rutony/RutonyPad/assets/images/2.webp

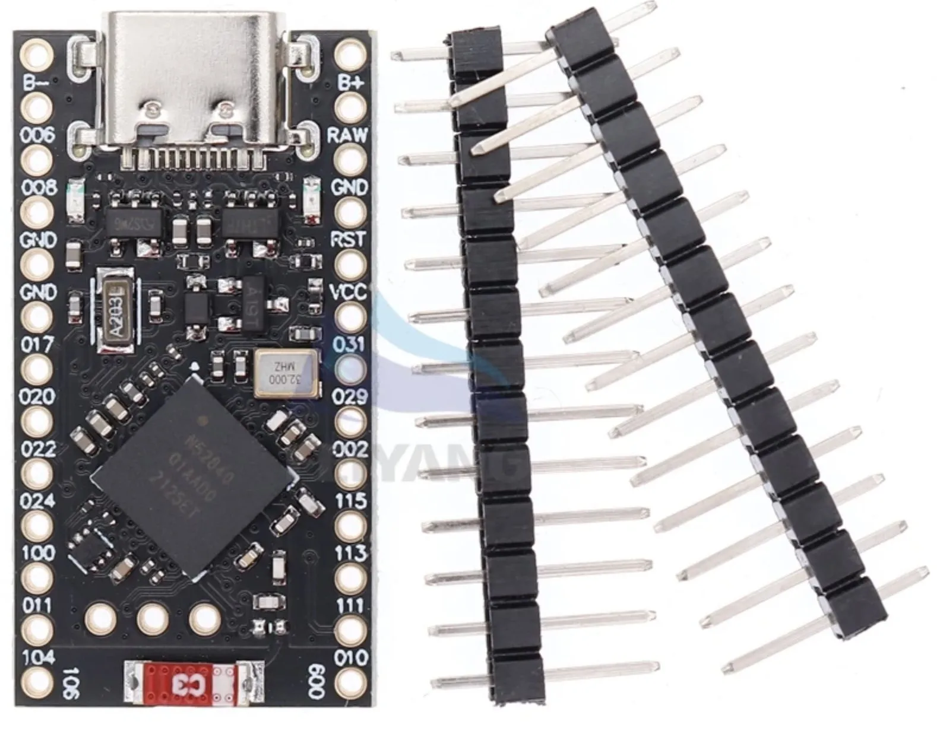
assets/images/2.webp
