rutony/RutonyPad/assets/images/3.jpg

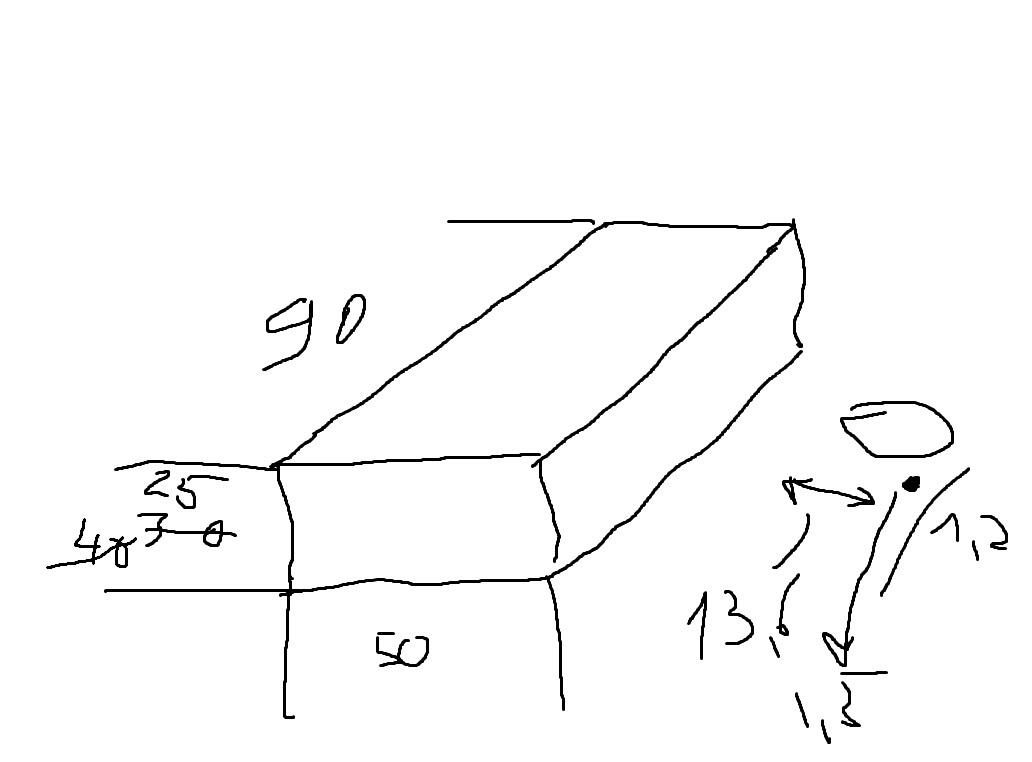
assets/images/3.jpg
