rutony/RutonyPad/assets/images/4.jpg

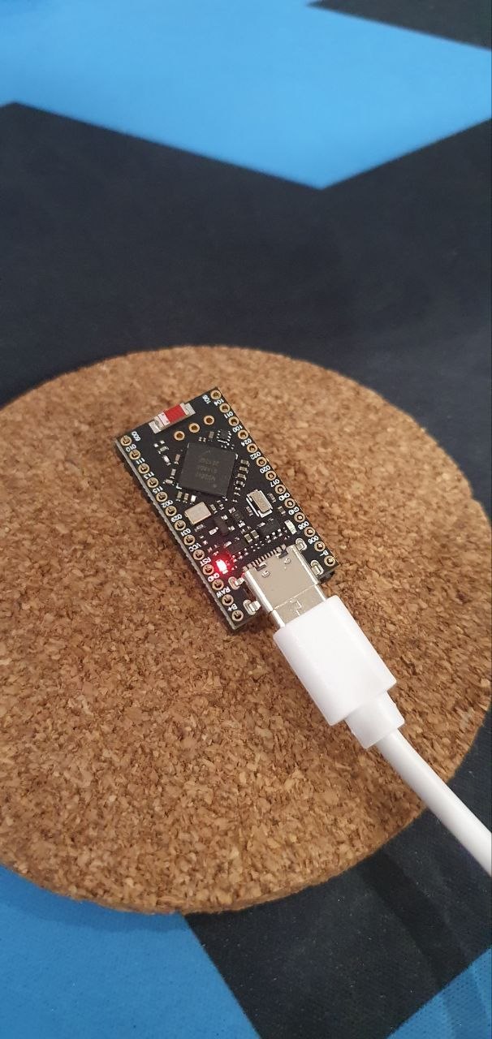
assets/images/4.jpg
