rutony/RutonyPad/assets/images/5.jpg

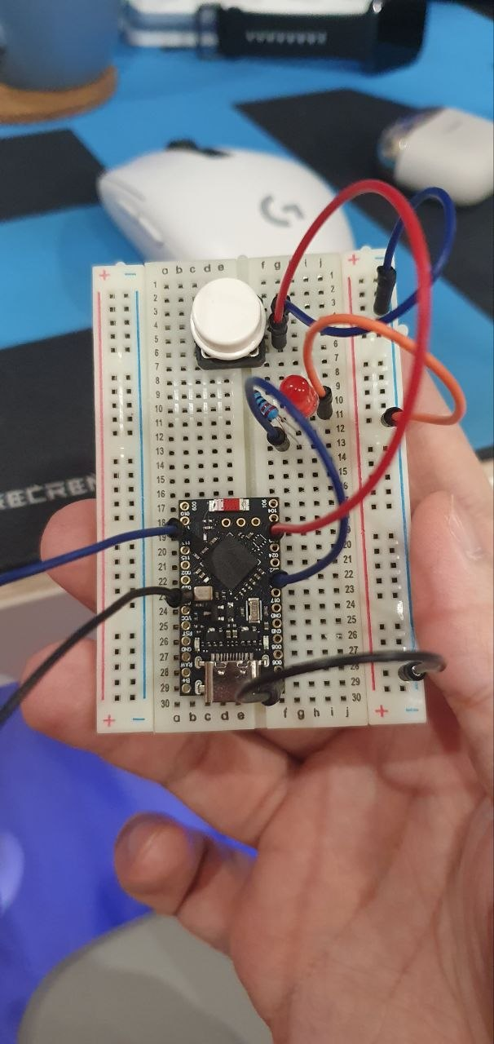
assets/images/5.jpg
