rutony/RutonyPad/assets/images/6.jpg

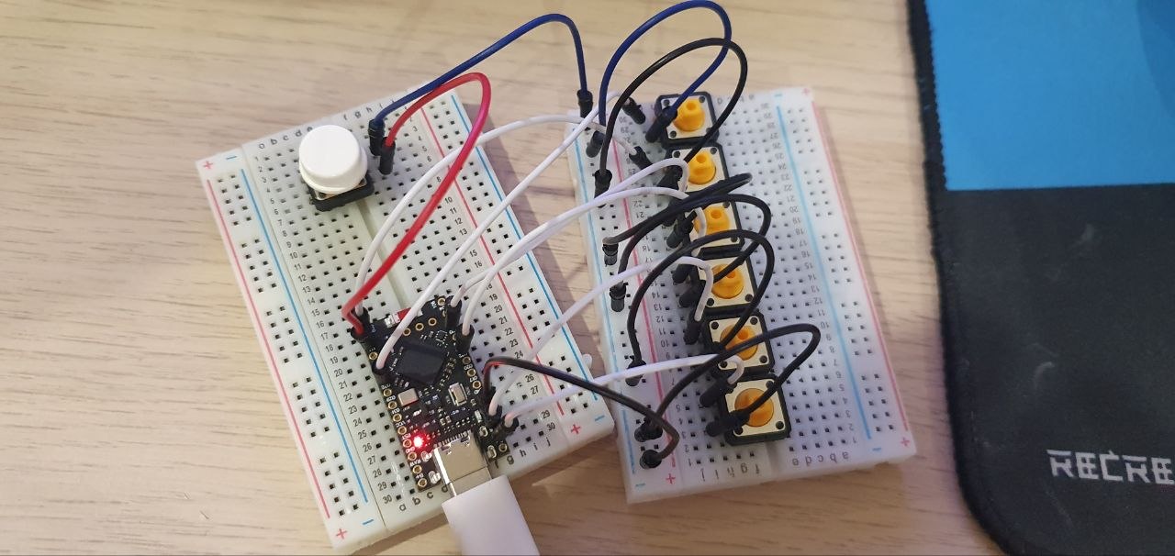
assets/images/6.jpg
