rutony/RutonyPad/assets/images/7.webp

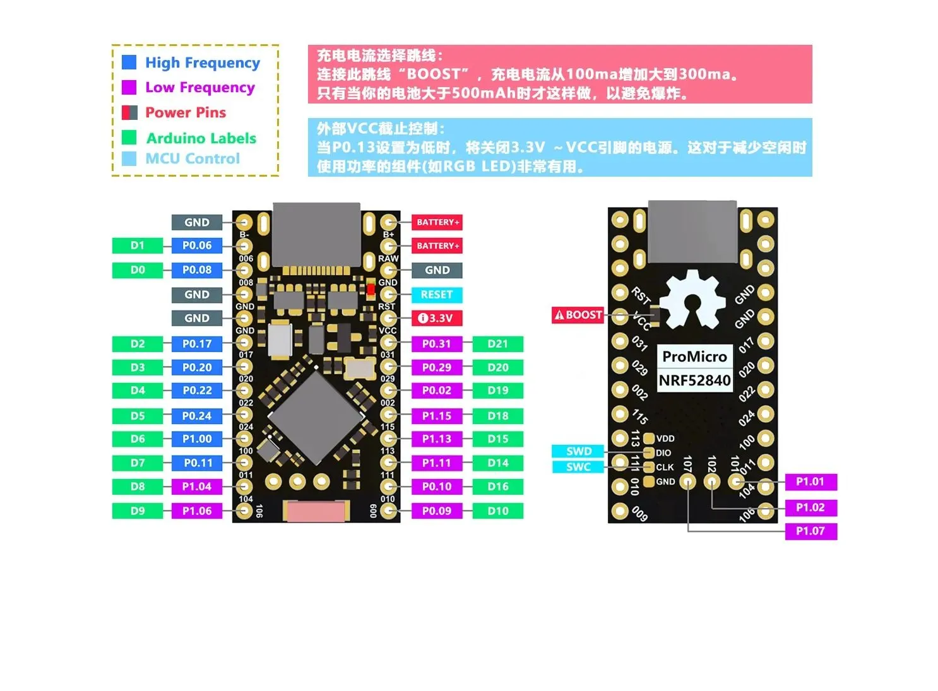
assets/images/7.webp
