rutony/RutonyPad/assets/images/9.png

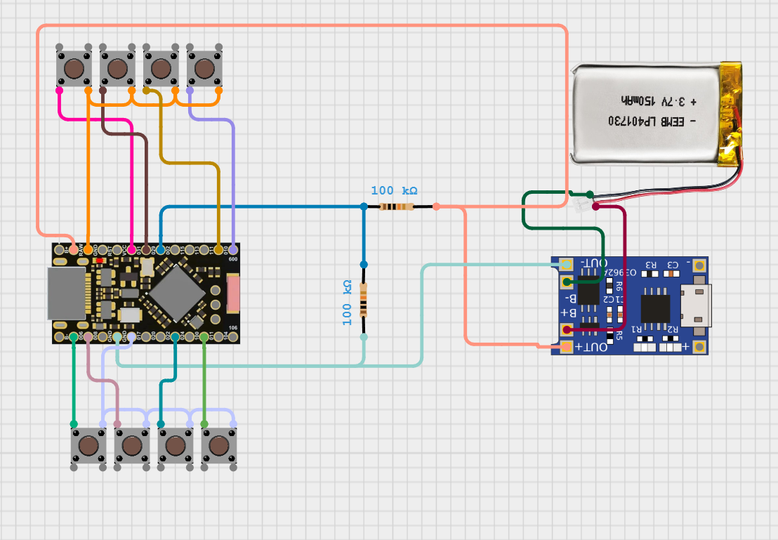
assets/images/9.png
