rutony/RutonyPad/assets/images/10.jpg

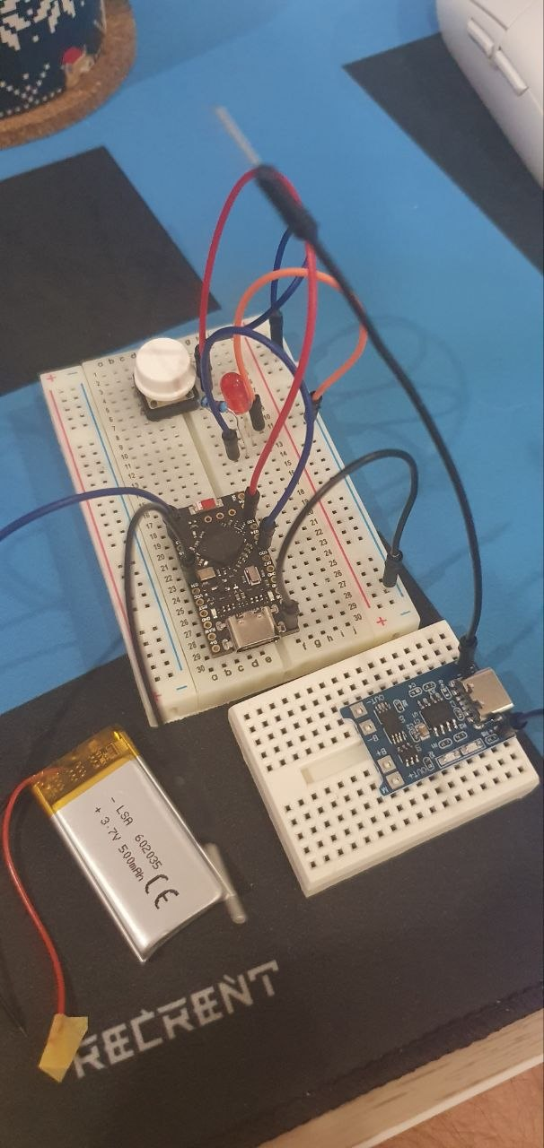
assets/images/10.jpg
