rutony/RutonyPad/assets/images/11.jpg

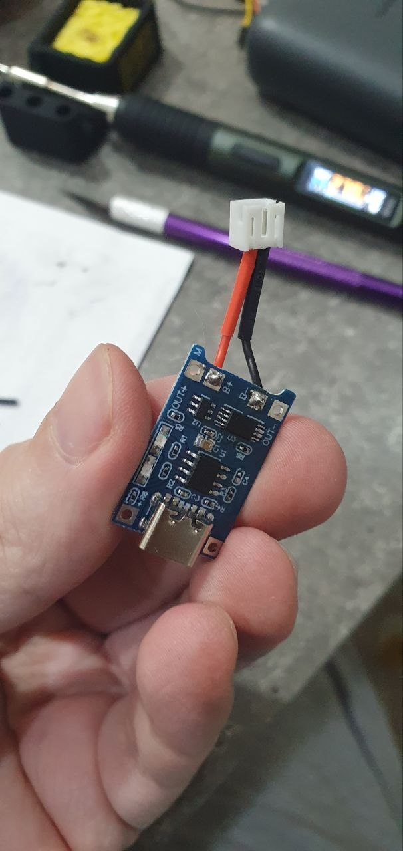
assets/images/11.jpg
