rutony/RutonyPad/assets/images/12.jpg

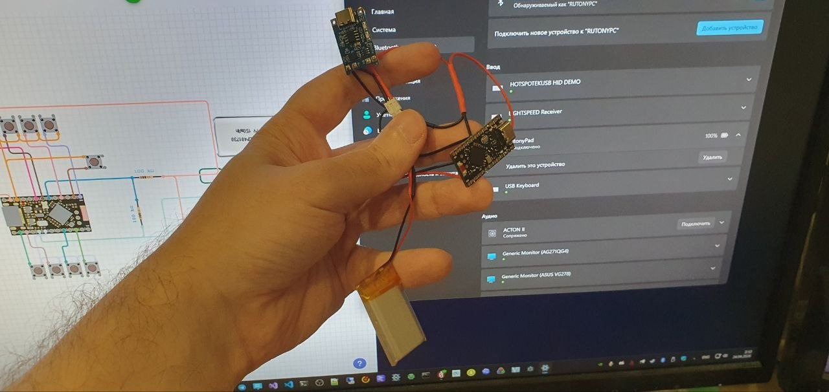
assets/images/12.jpg
