rutony/RutonyPad/assets/images/13.jpg

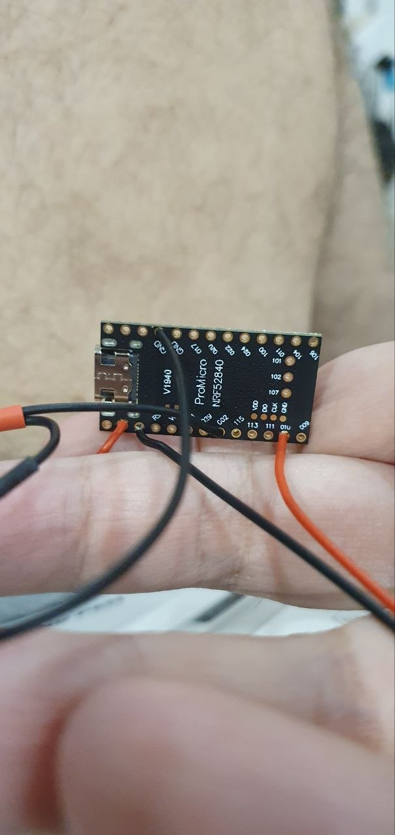
assets/images/13.jpg
