rutony/RutonyPad/assets/images/14.jpg

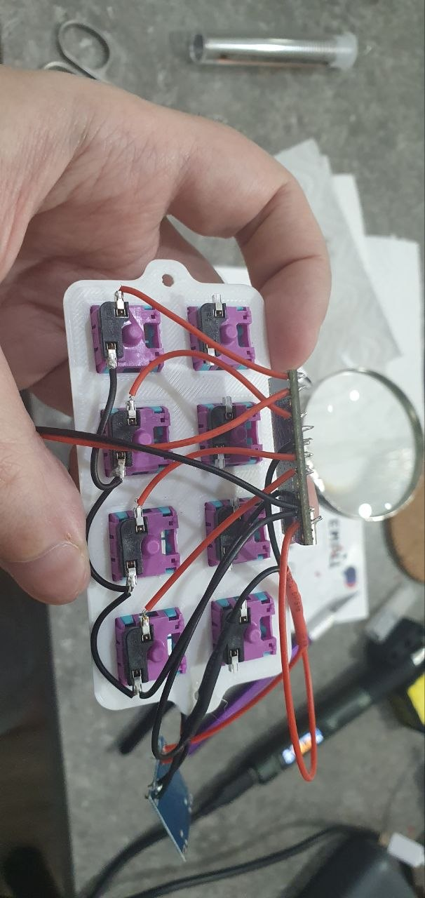
assets/images/14.jpg
