rutony/RutonyPad/assets/images/15.jpg

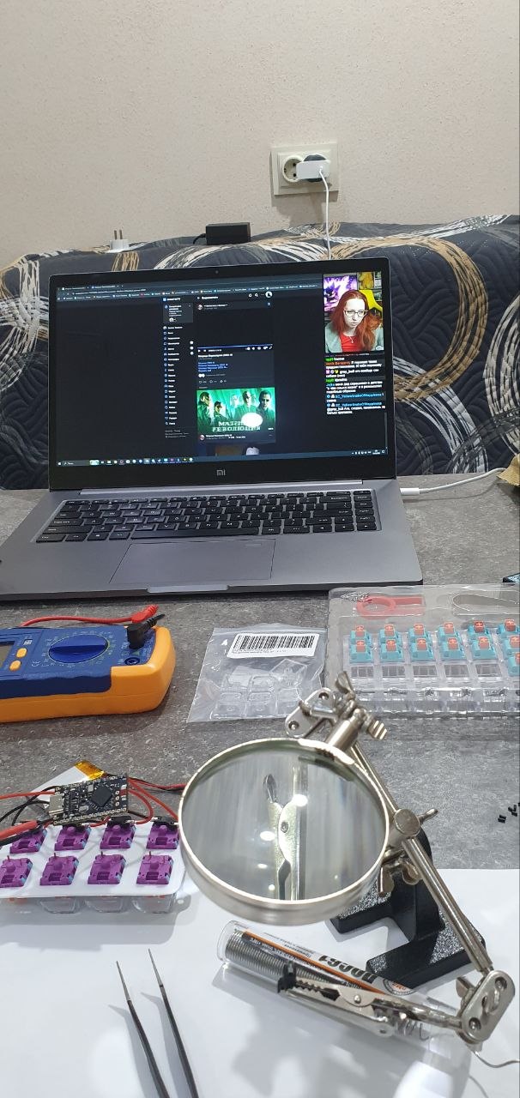
assets/images/15.jpg
