rutony/RutonyPad/assets/images/16.jpg

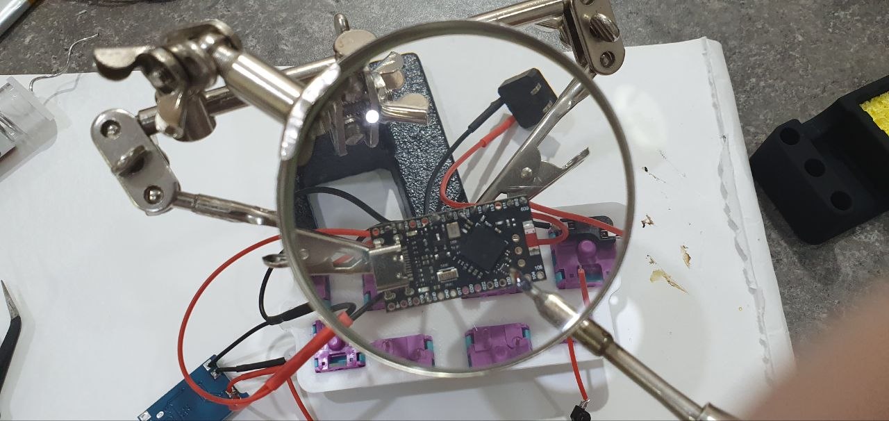
assets/images/16.jpg
