rutony/RutonyPad/assets/images/17.jpg

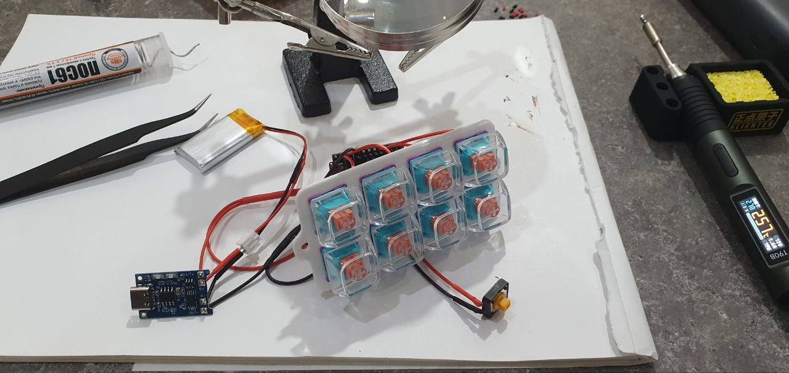
assets/images/17.jpg
