rutony/RutonyPad/assets/images/18.jpg

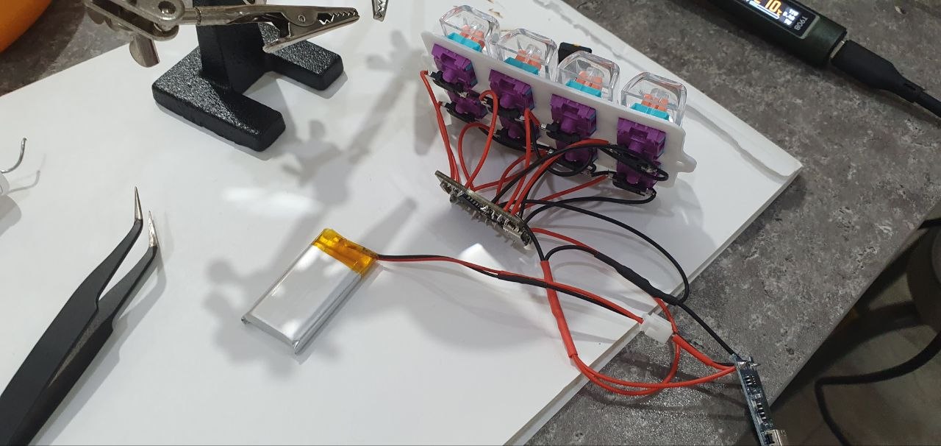
assets/images/18.jpg
