rutony/RutonyPad/assets/images/19.jpg

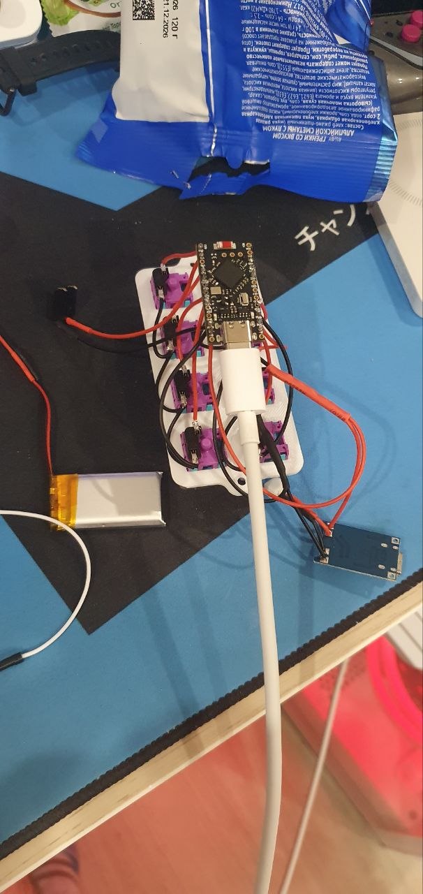
assets/images/19.jpg
