rutony/RutonyPad/assets/images/21.jpg

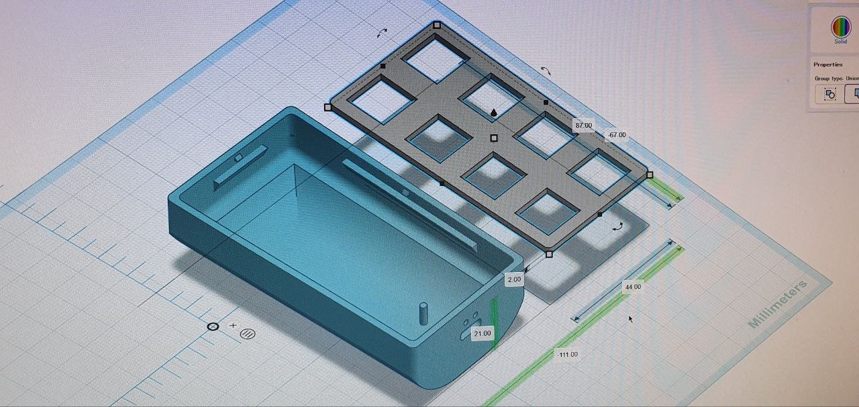
assets/images/21.jpg
