rutony/RutonyPad/assets/images/22.jpg

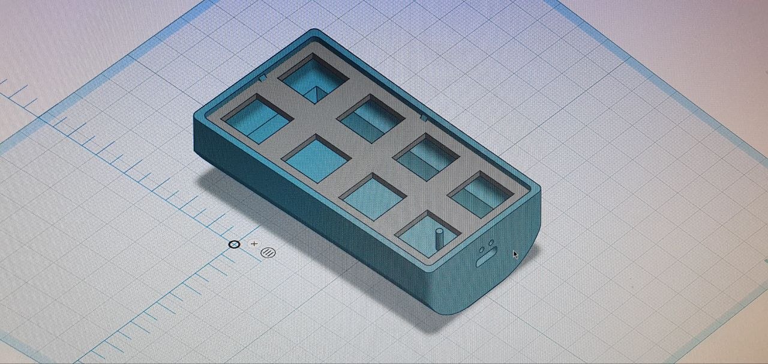
assets/images/22.jpg
