rutony/RutonyPad/assets/images/23.jpg

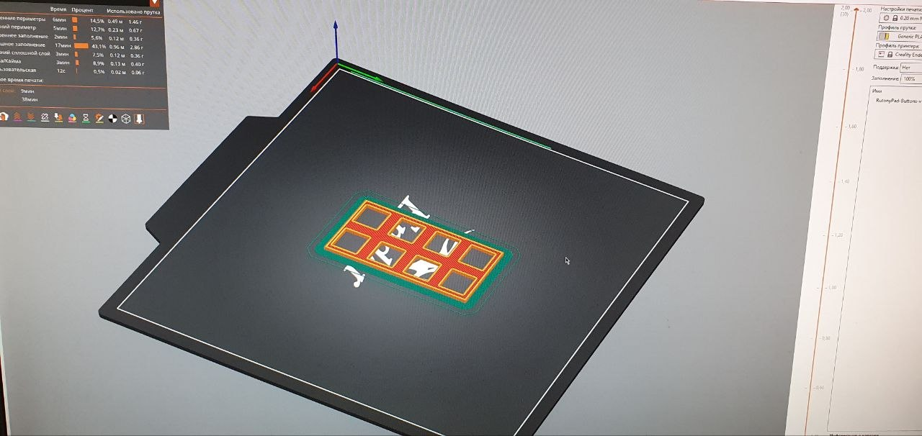
assets/images/23.jpg
