rutony/RutonyPad/assets/images/24.jpg

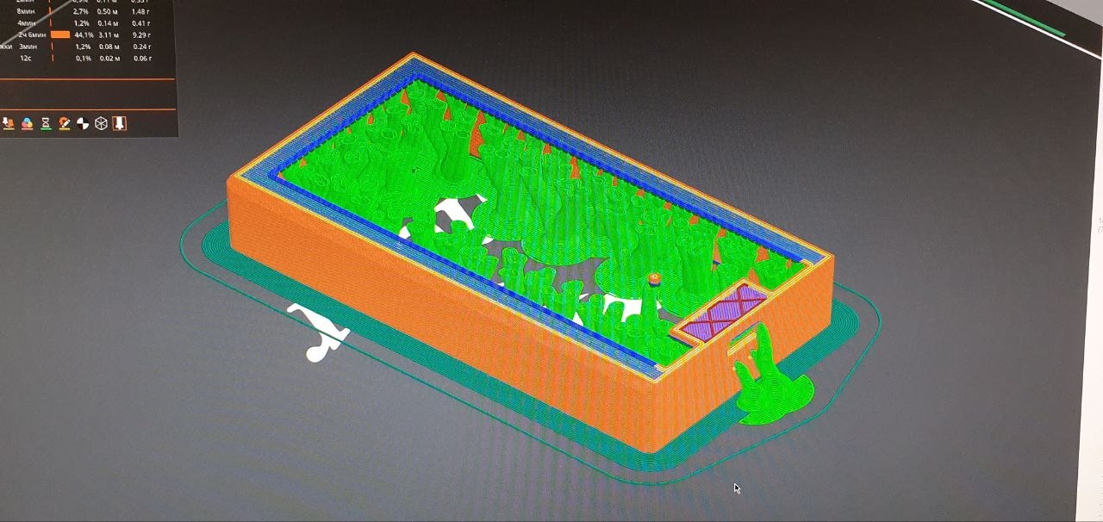
assets/images/24.jpg
