rutony/RutonyPad/assets/images/25.jpg

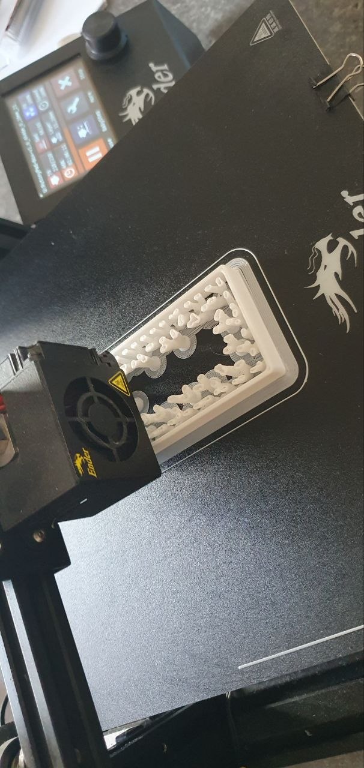
assets/images/25.jpg
