rutony/RutonyPad/assets/images/26.jpg

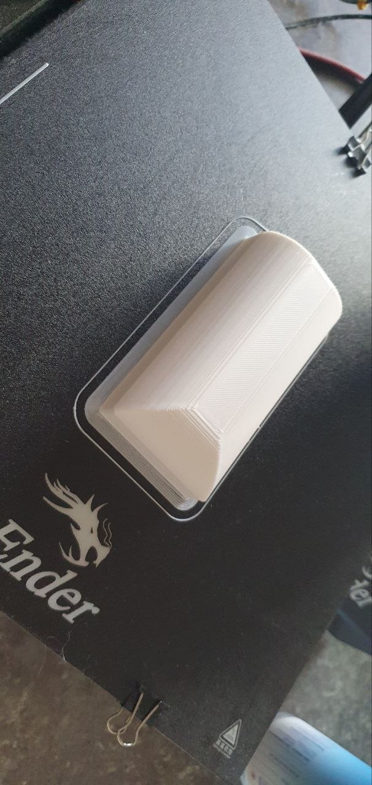
assets/images/26.jpg
