rutony/RutonyPad/assets/images/27.jpg

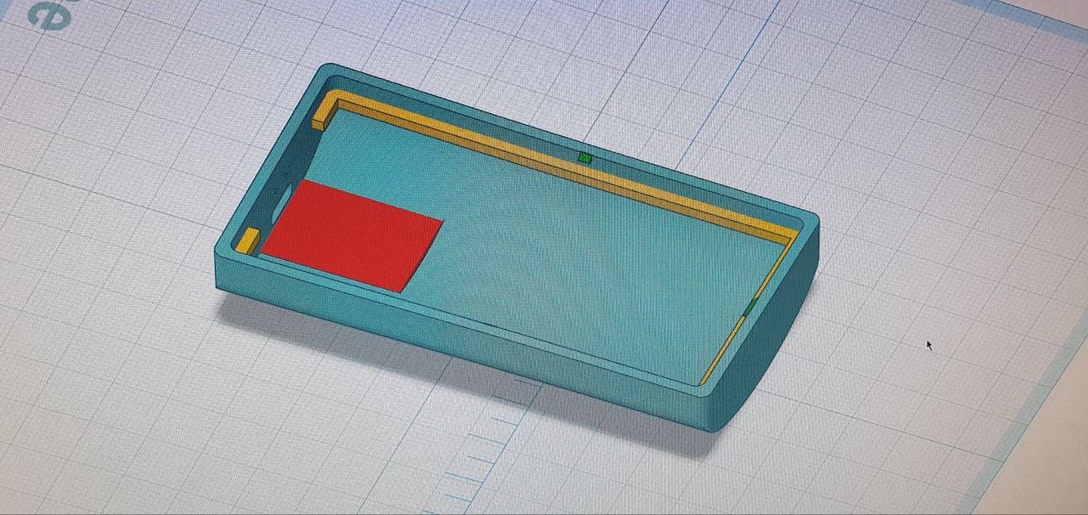
assets/images/27.jpg
