rutony/RutonyPad/assets/images/28.png

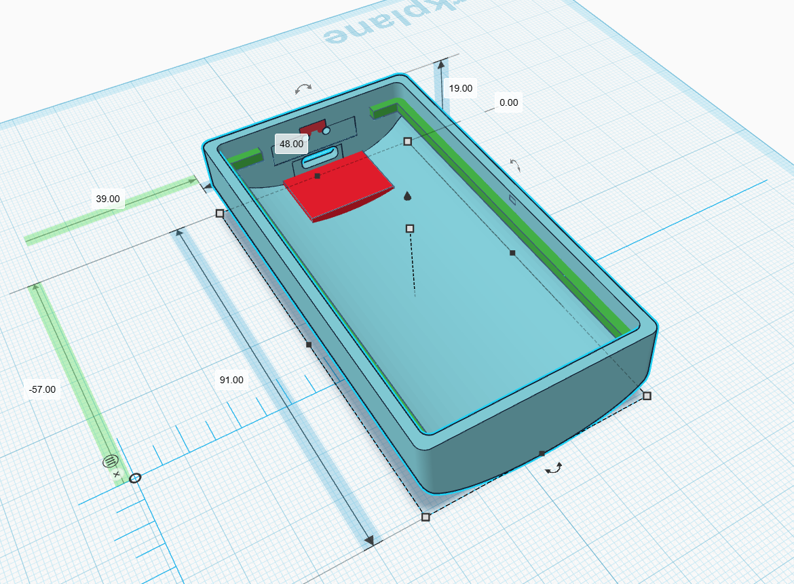
assets/images/28.png
