rutony/RutonyPad/assets/images/29.jpg

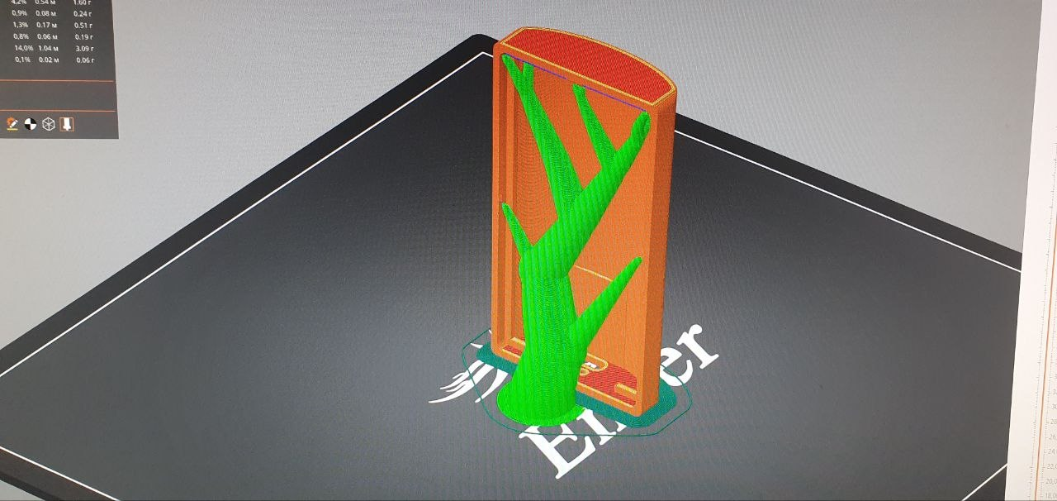
assets/images/29.jpg
