rutony/RutonyPad/assets/images/30.jpg

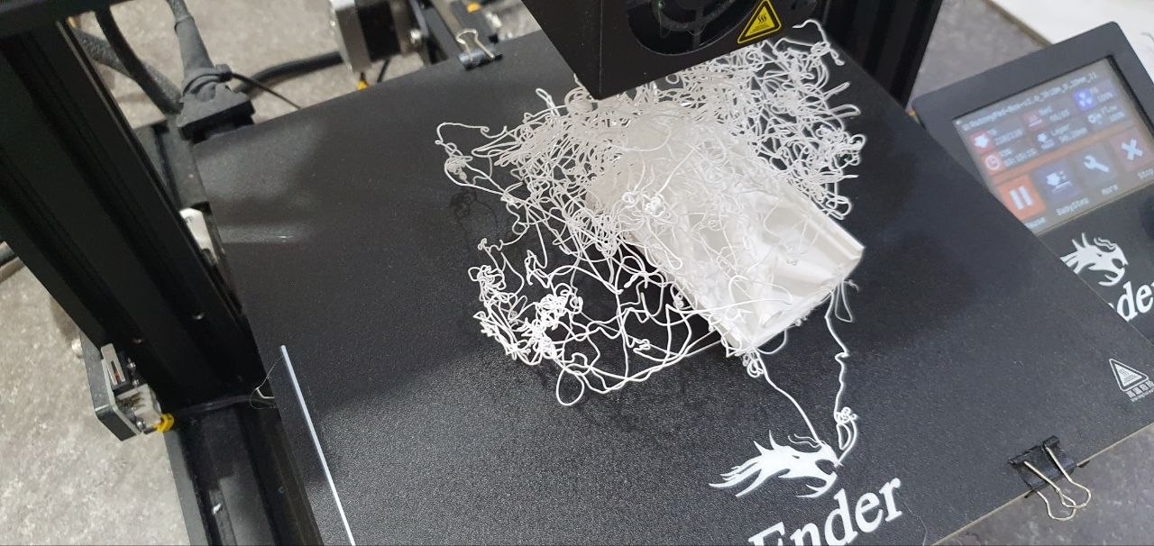
assets/images/30.jpg
