rutony/RutonyPad/assets/images/31.jpg

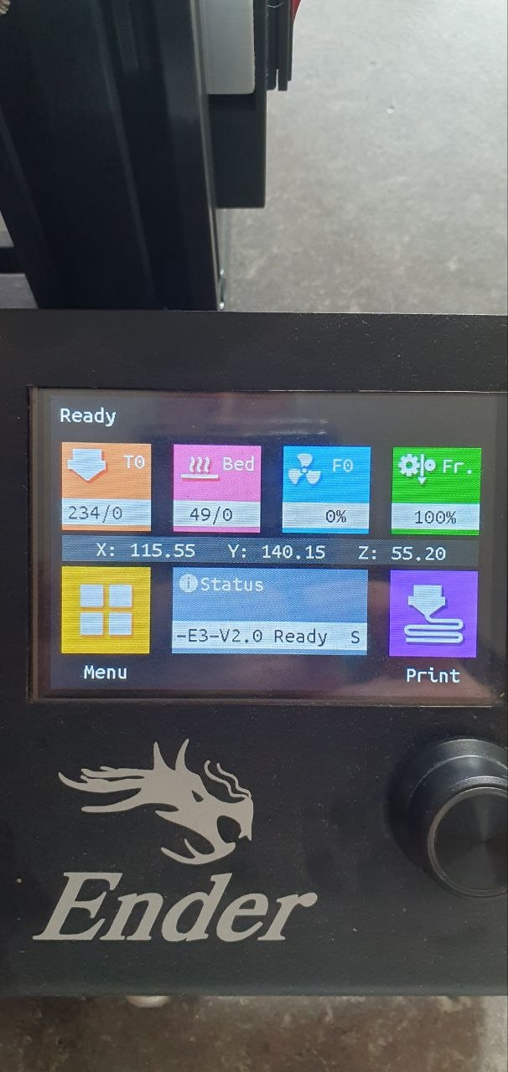
assets/images/31.jpg
