rutony/RutonyPad/assets/images/32.jpg

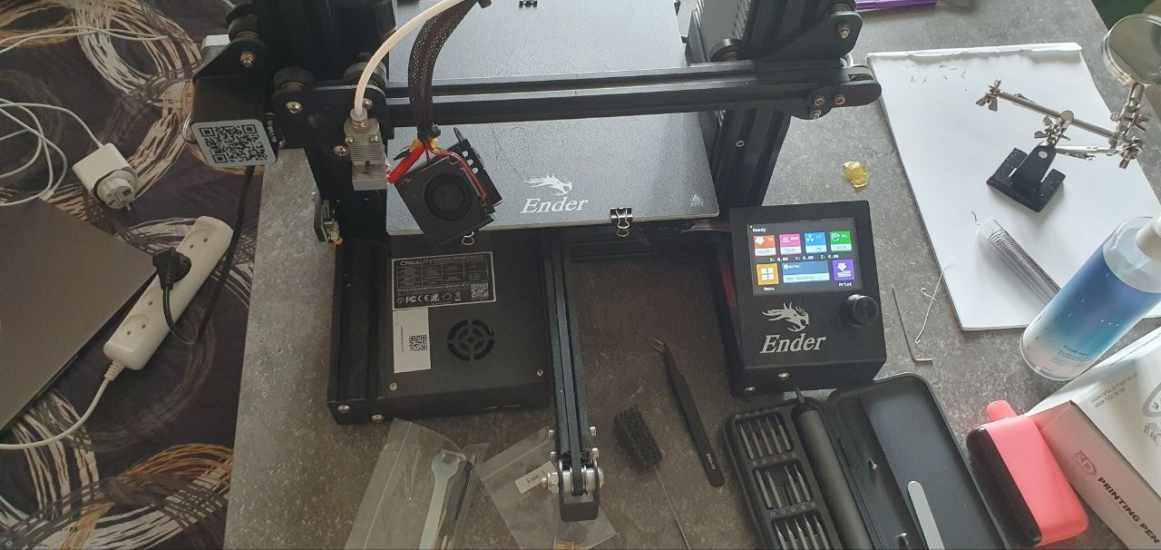
assets/images/32.jpg
