rutony/RutonyPad/assets/images/33.jpg

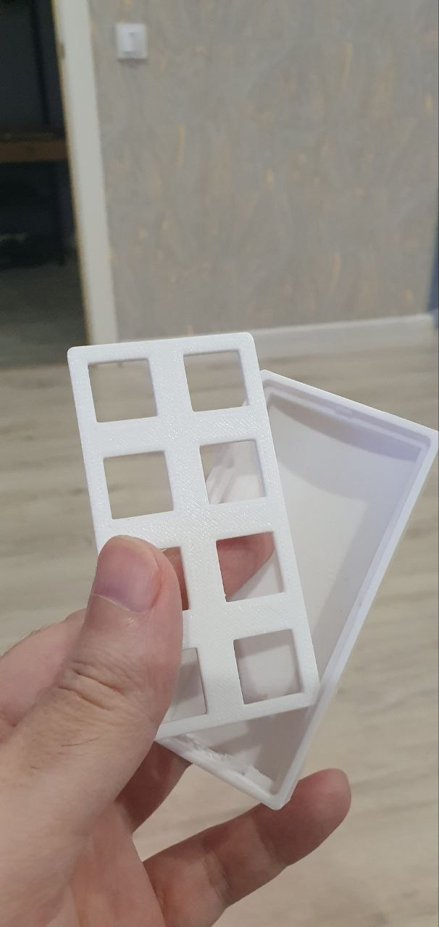
assets/images/33.jpg
