rutony/RutonyPad/assets/images/34.jpg

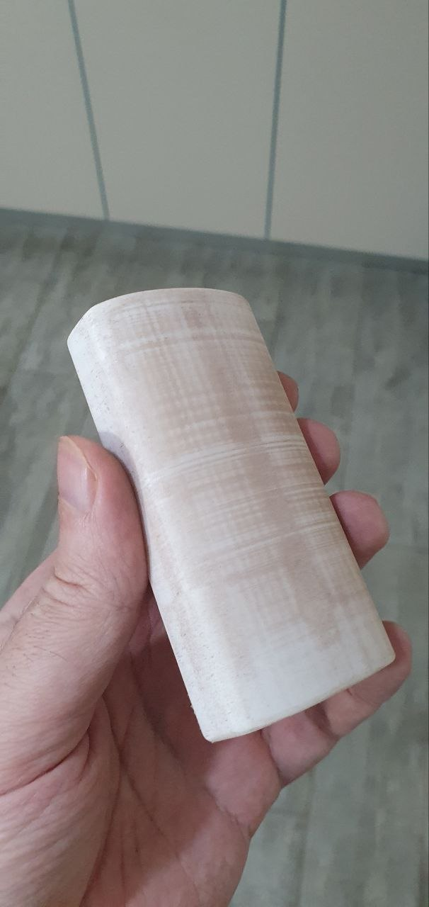
assets/images/34.jpg
