rutony/RutonyPad/assets/images/35.jpg

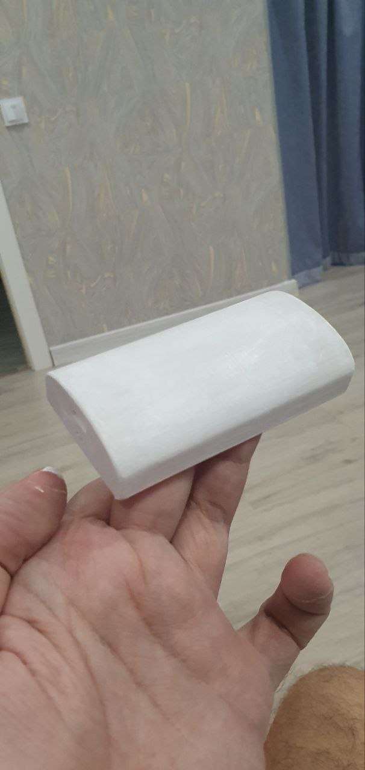
assets/images/35.jpg
