rutony/RutonyPad/assets/images/36.jpg

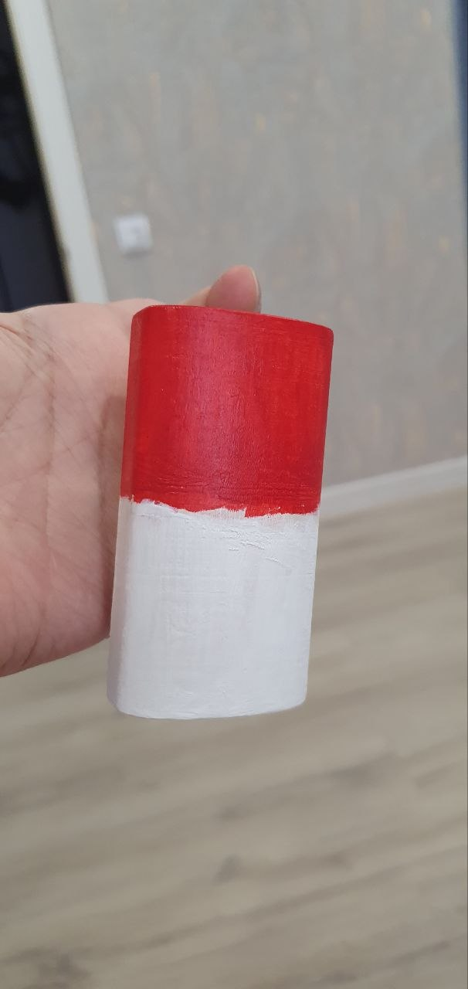
assets/images/36.jpg
