rutony/RutonyPad/assets/images/37.jpg

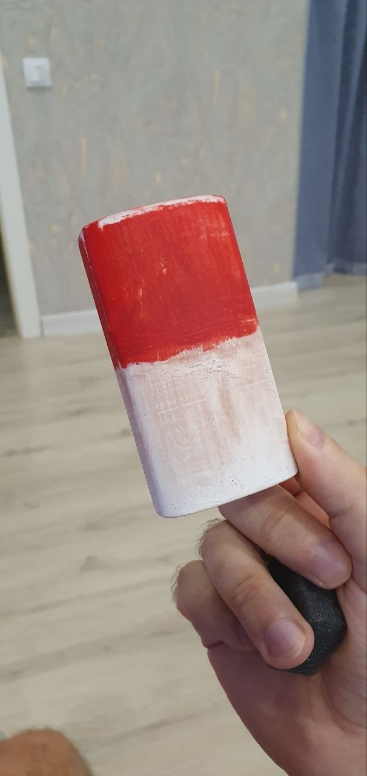
assets/images/37.jpg
