rutony/RutonyPad/assets/images/38.jpg

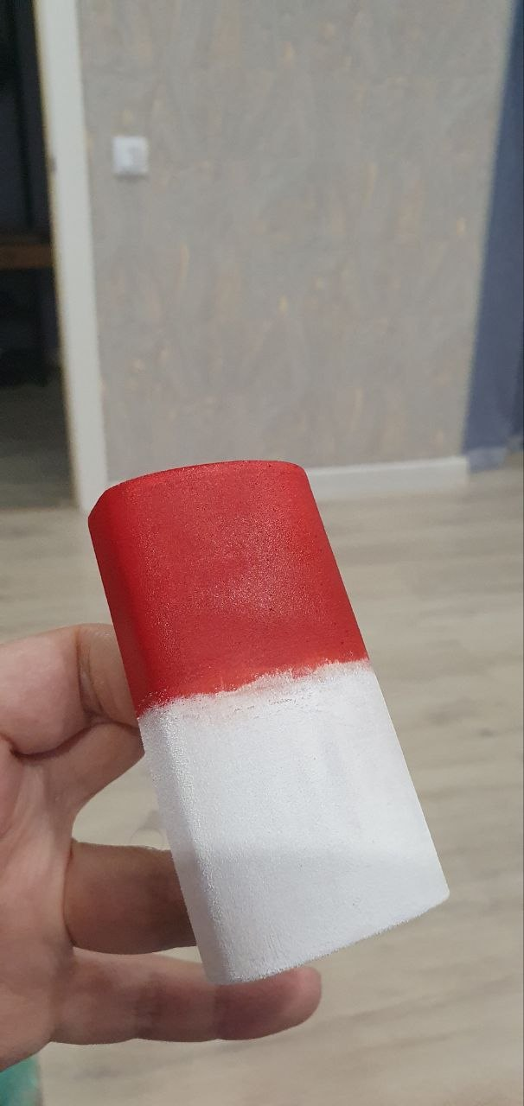
assets/images/38.jpg
