rutony/RutonyPad/assets/images/39.jpg

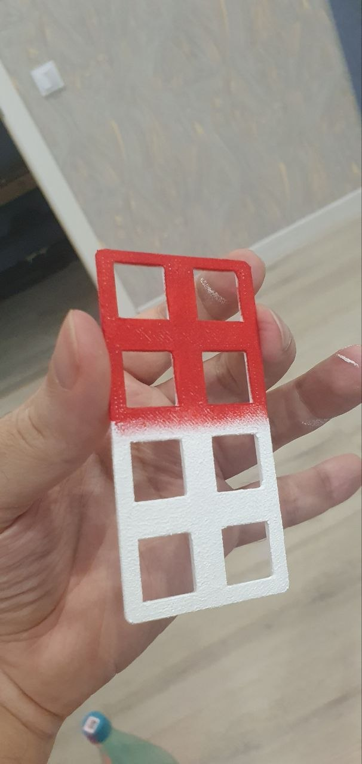
assets/images/39.jpg
