rutony/RutonyPad/assets/images/40.jpg

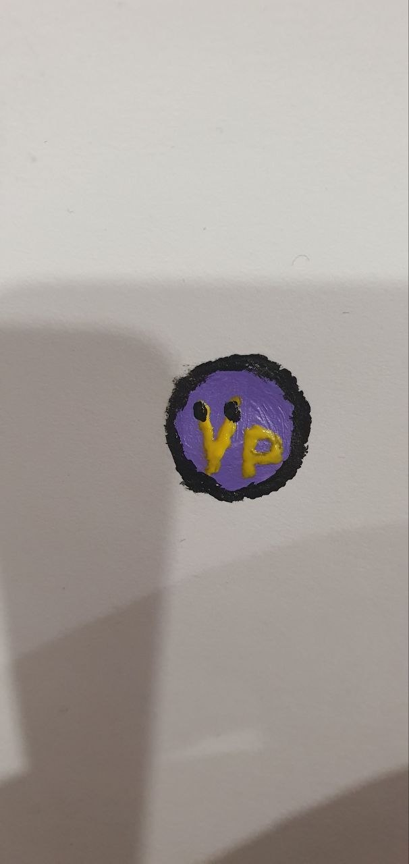
assets/images/40.jpg
