rutony/RutonyPad/assets/images/41.jpg

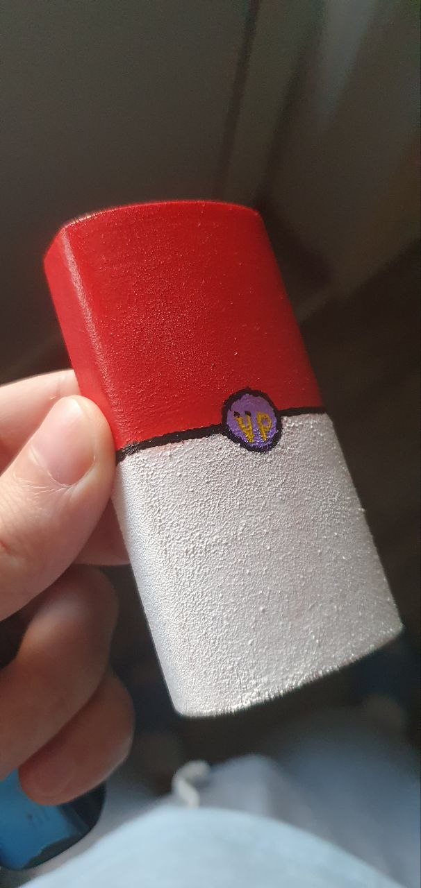
assets/images/41.jpg
