rutony/RutonyPad/assets/images/42.jpg

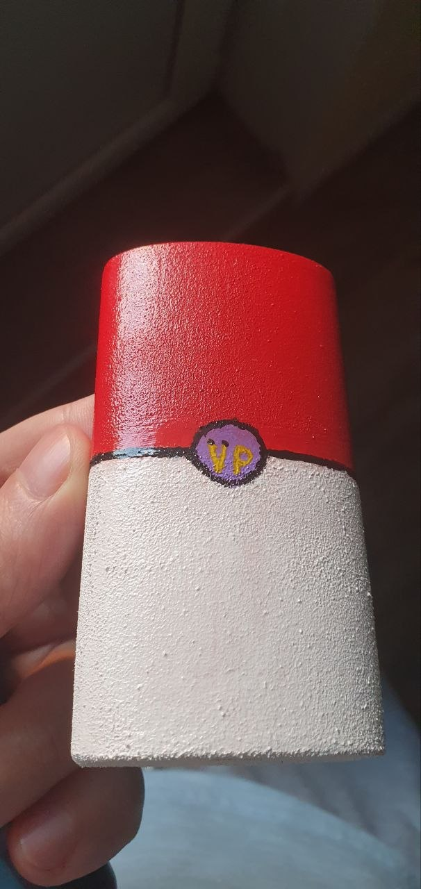
assets/images/42.jpg
