rutony/RutonyPad/assets/images/43.jpg

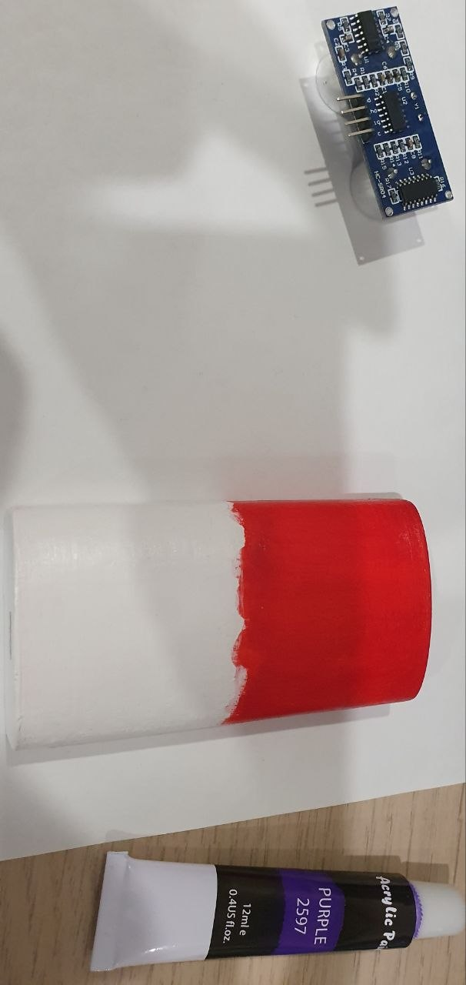
assets/images/43.jpg
