rutony/RutonyPad/assets/images/44.jpg

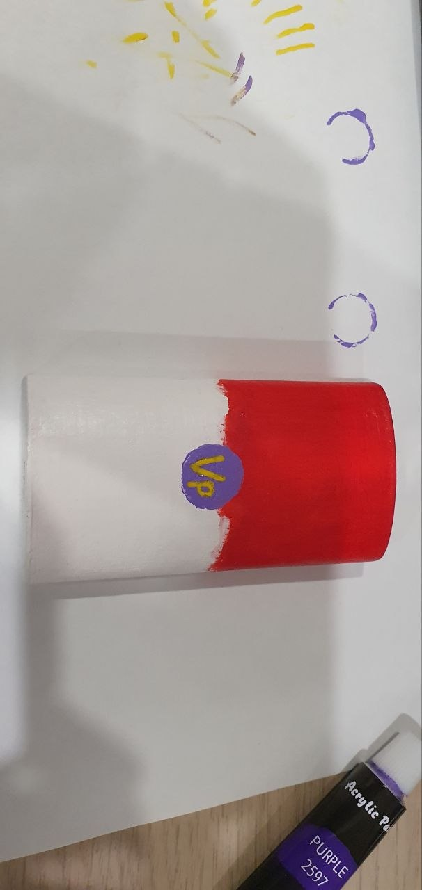
assets/images/44.jpg
