rutony/RutonyPad/assets/images/45.jpg

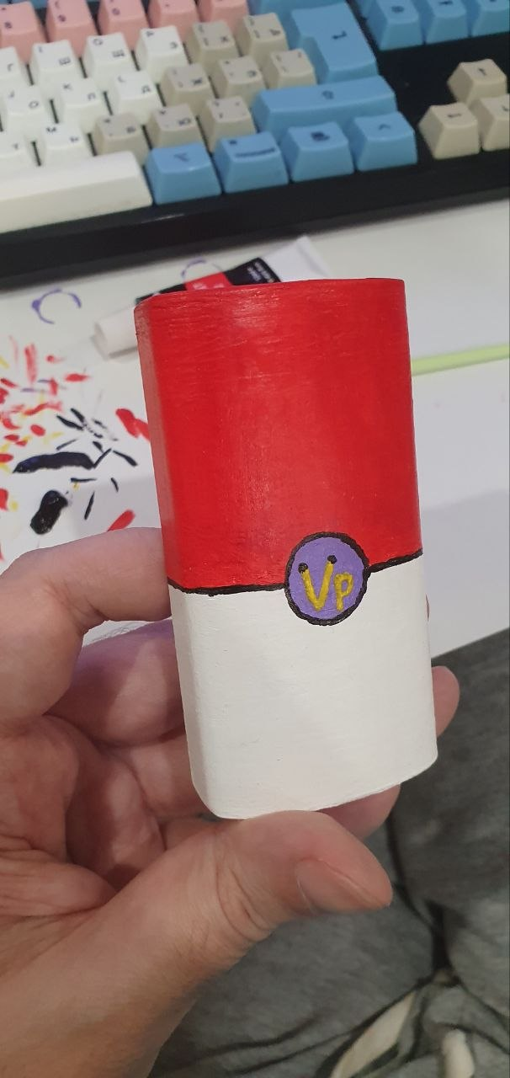
assets/images/45.jpg
