rutony/RutonyPad/assets/images/46.jpg

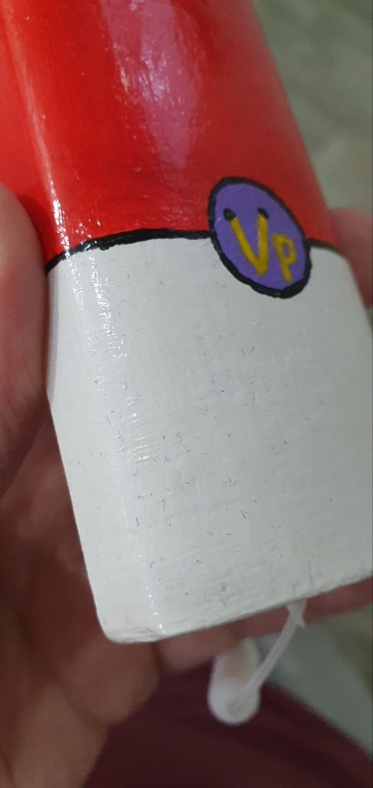
assets/images/46.jpg
