rutony/RutonyPad/assets/images/47.jpg

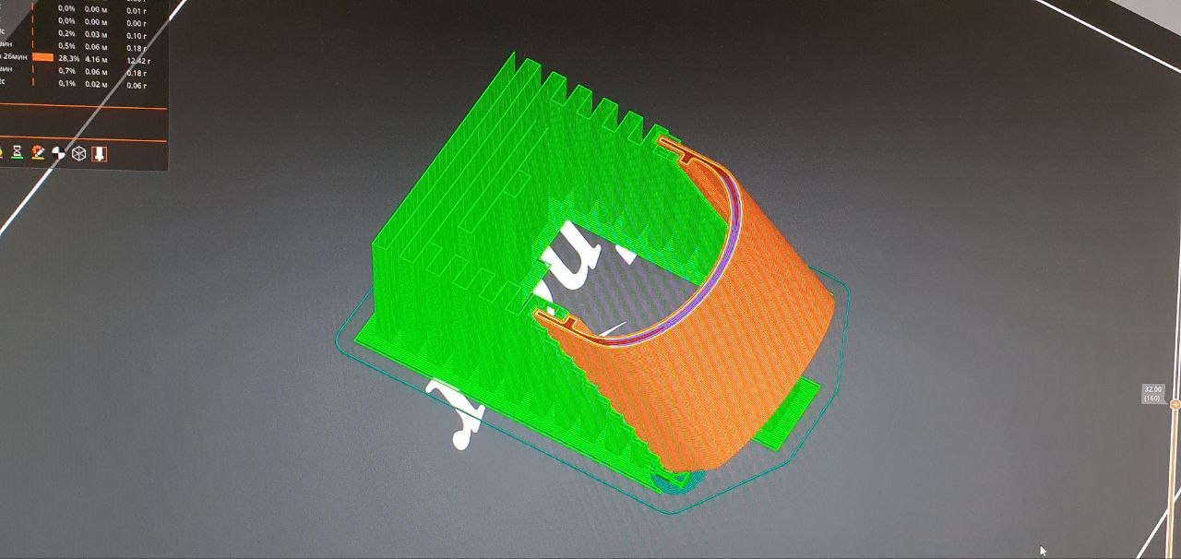
assets/images/47.jpg
