rutony/RutonyPad/assets/images/48.jpg

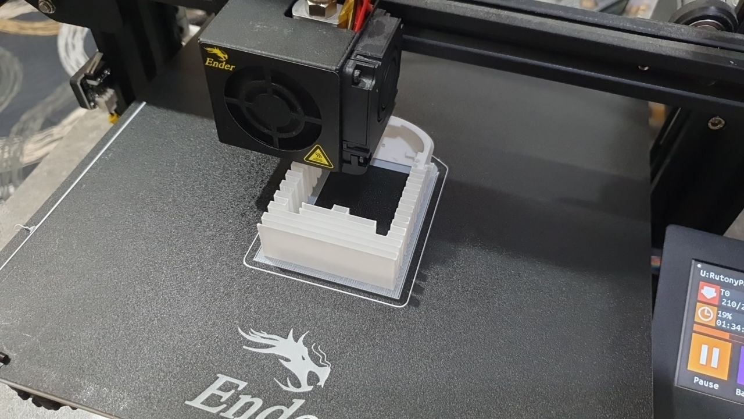
assets/images/48.jpg
