rutony/RutonyPad/assets/images/49.jpg

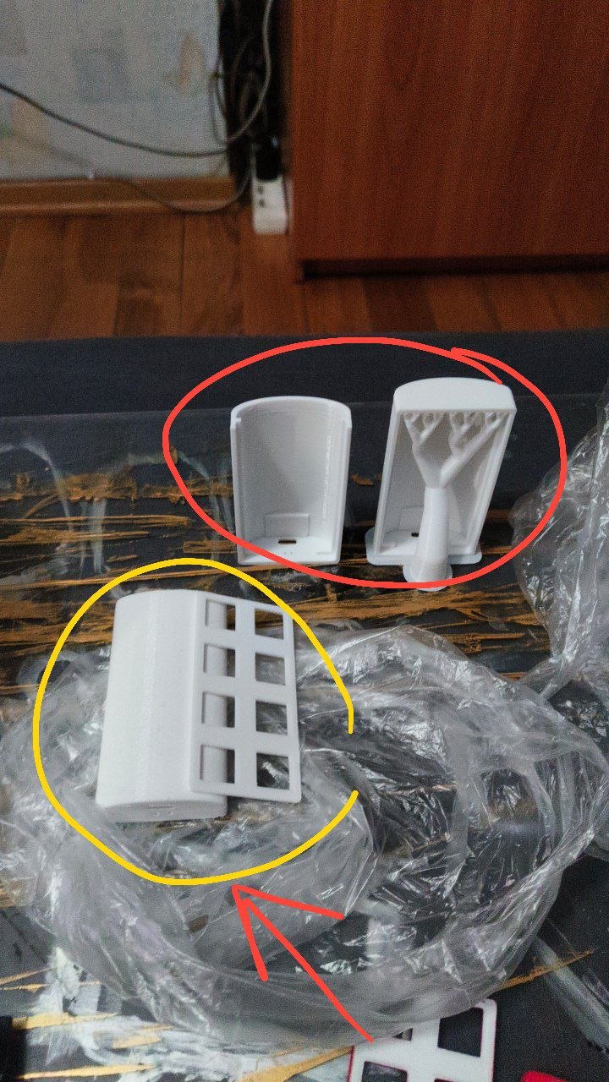
assets/images/49.jpg
