rutony/RutonyPad/assets/images/50.jpg

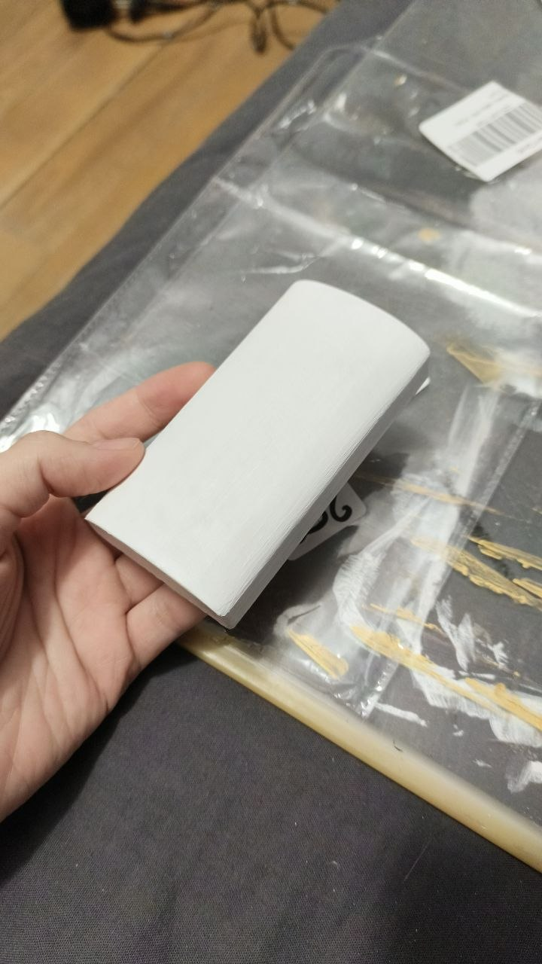
assets/images/50.jpg
