rutony/RutonyPad/assets/images/51.jpg

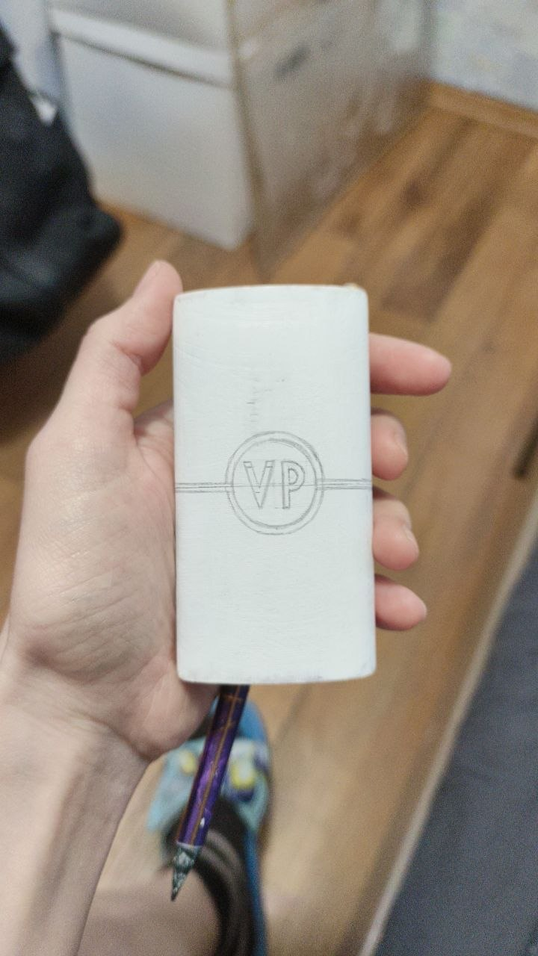
assets/images/51.jpg
