rutony/RutonyPad/assets/images/52.jpg

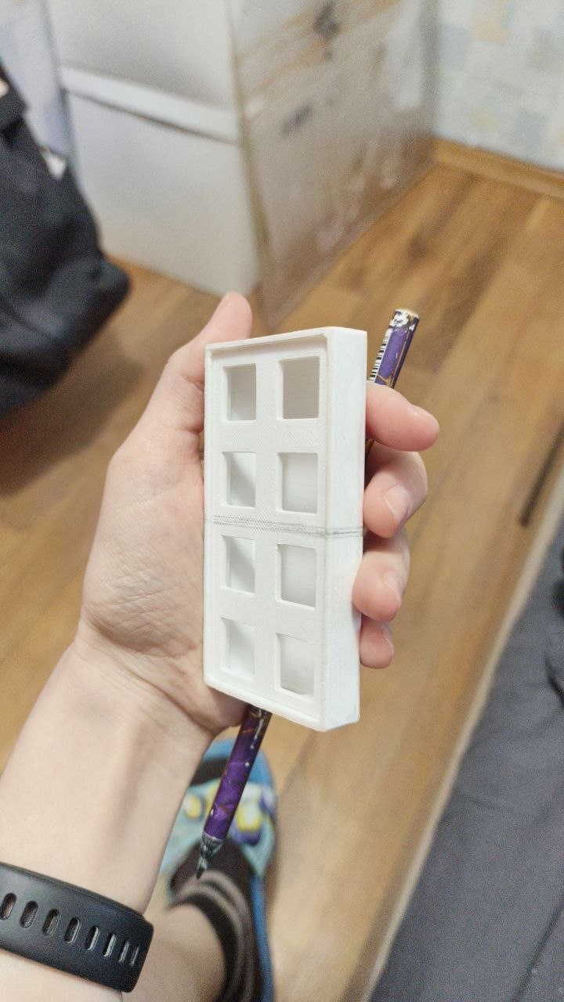
assets/images/52.jpg
