rutony/RutonyPad/assets/images/53.jpg

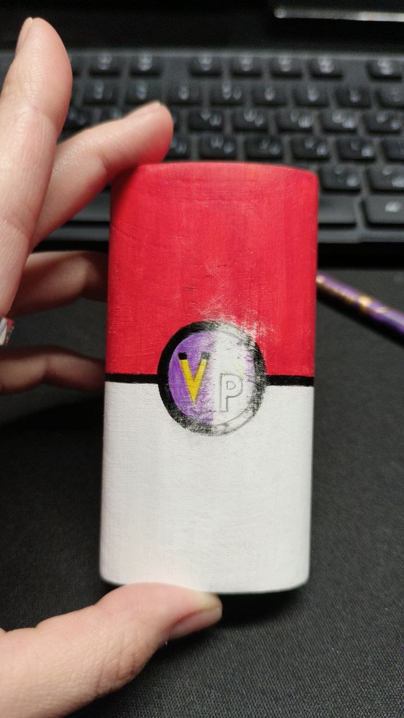
assets/images/53.jpg
