rutony/RutonyPad/assets/images/54.jpg

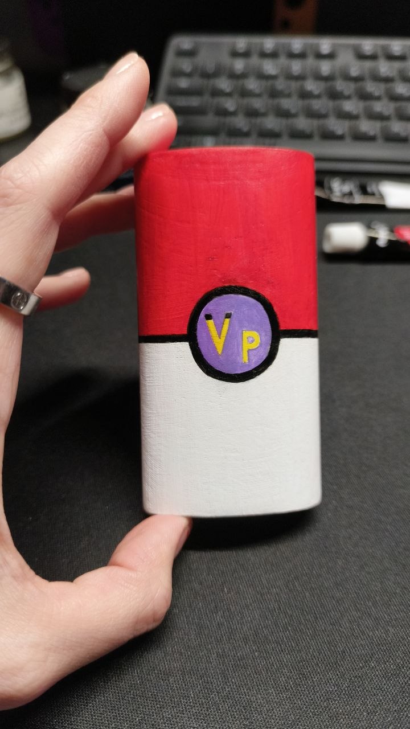
assets/images/54.jpg
