rutony/RutonyPad/assets/images/55.jpg

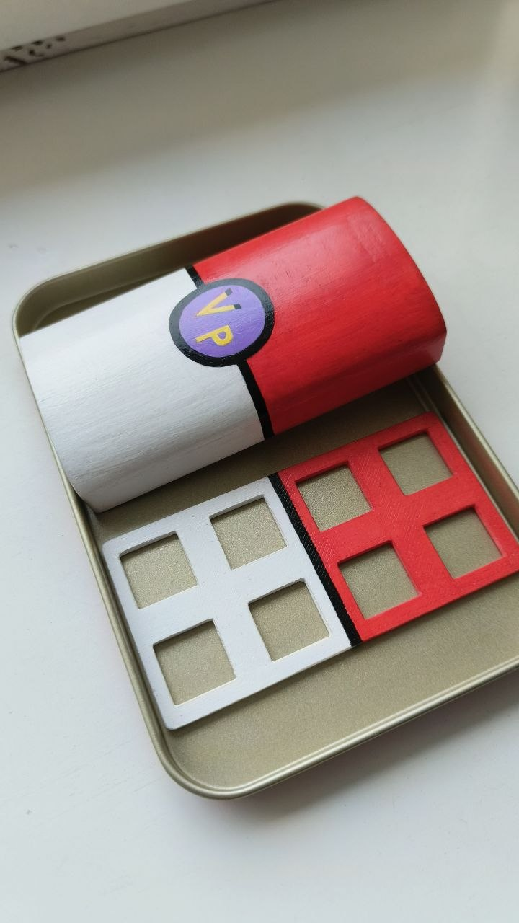
assets/images/55.jpg
