rutony/RutonyPad/assets/images/56.jpg

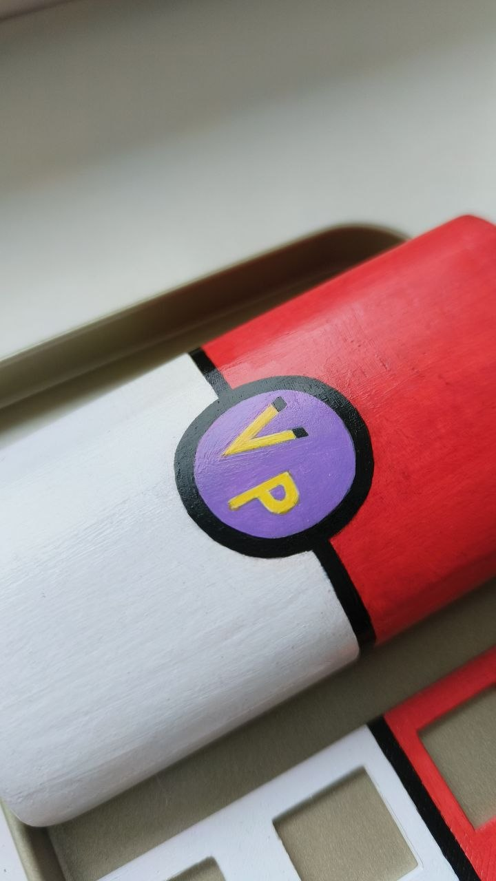
assets/images/56.jpg
