rutony/RutonyPad/assets/images/57.jpg

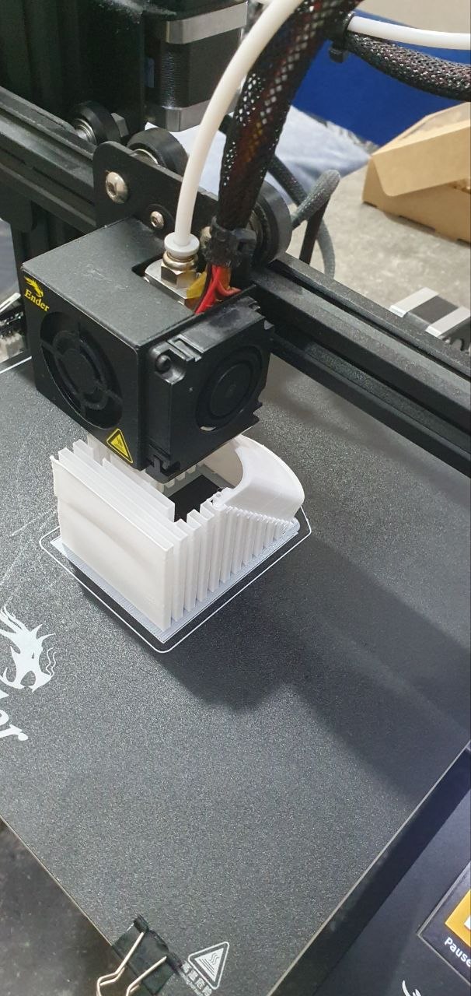
assets/images/57.jpg
