rutony/RutonyPad/assets/images/58.jpg

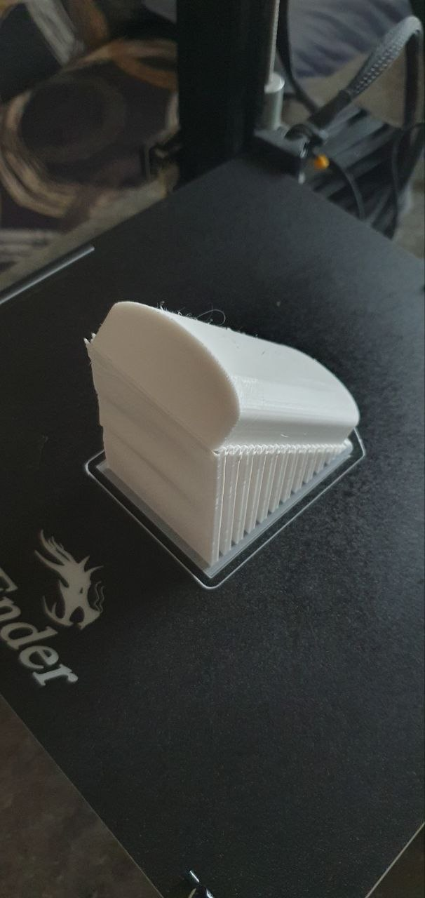
assets/images/58.jpg
