rutony/RutonyPad/assets/images/59.jpg

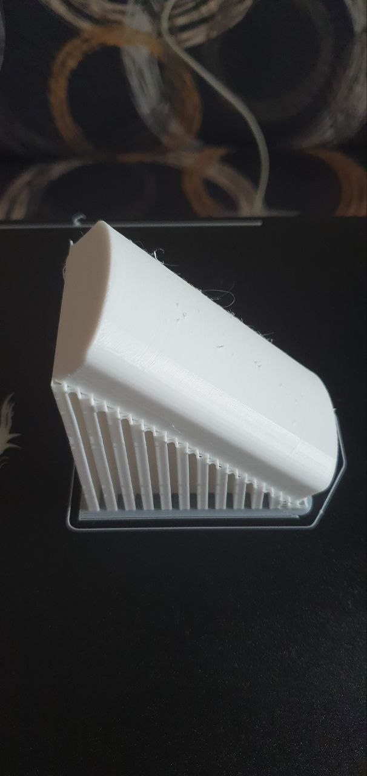
assets/images/59.jpg
