rutony/RutonyPad/assets/images/60.jpg

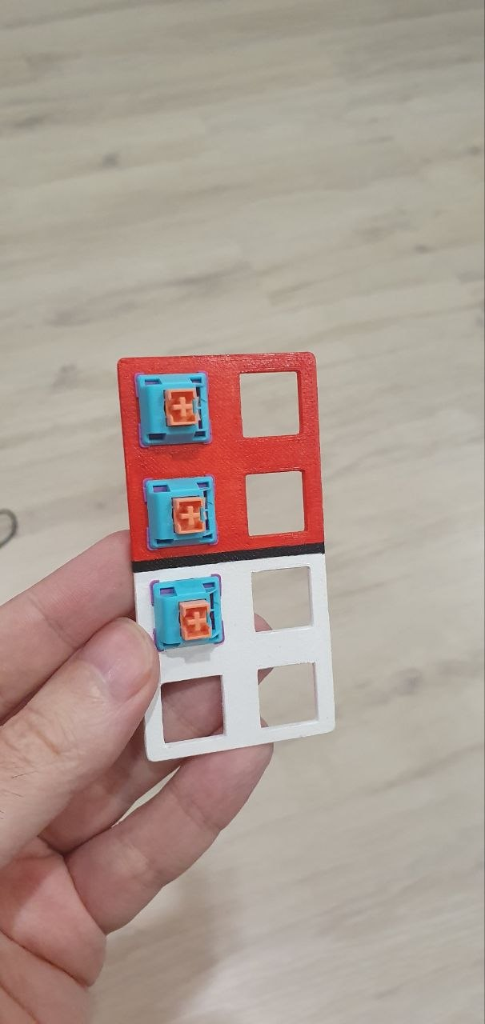
assets/images/60.jpg
