rutony/RutonyPad/assets/images/61.jpg

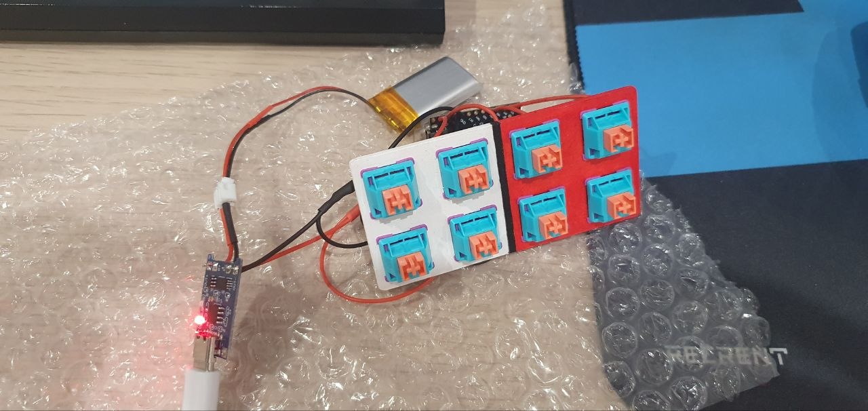
assets/images/61.jpg
