rutony/RutonyPad/assets/images/62.jpg

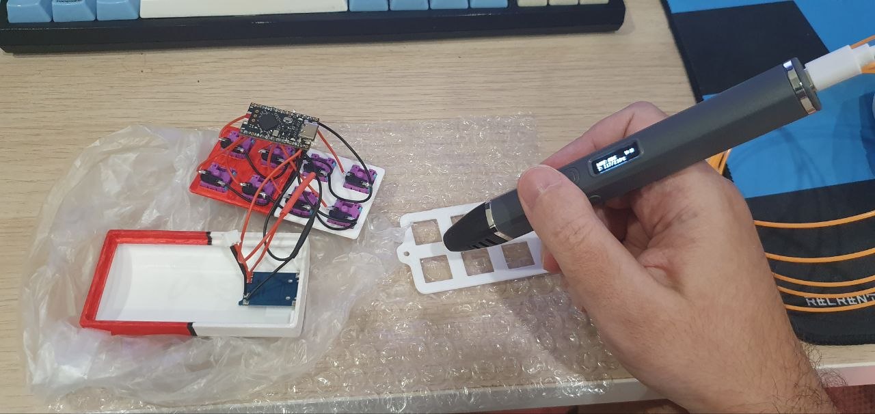
assets/images/62.jpg
