rutony/RutonyPad/assets/images/63.jpg

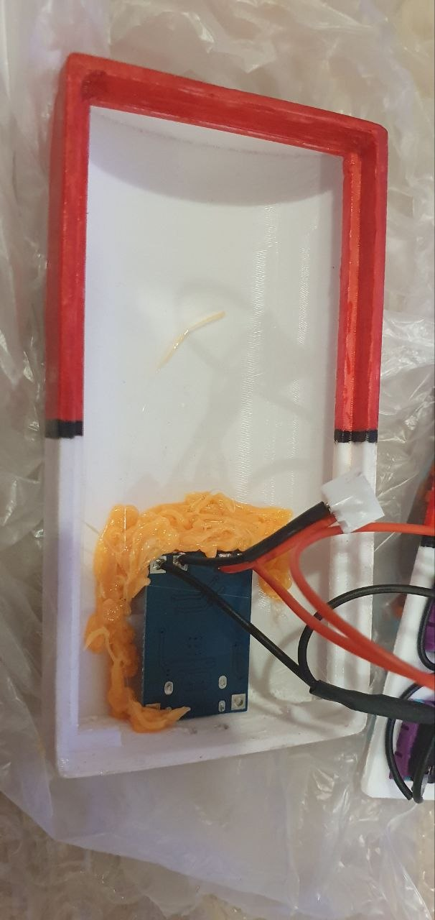
assets/images/63.jpg
