rutony/RutonyPad/assets/images/64.jpg

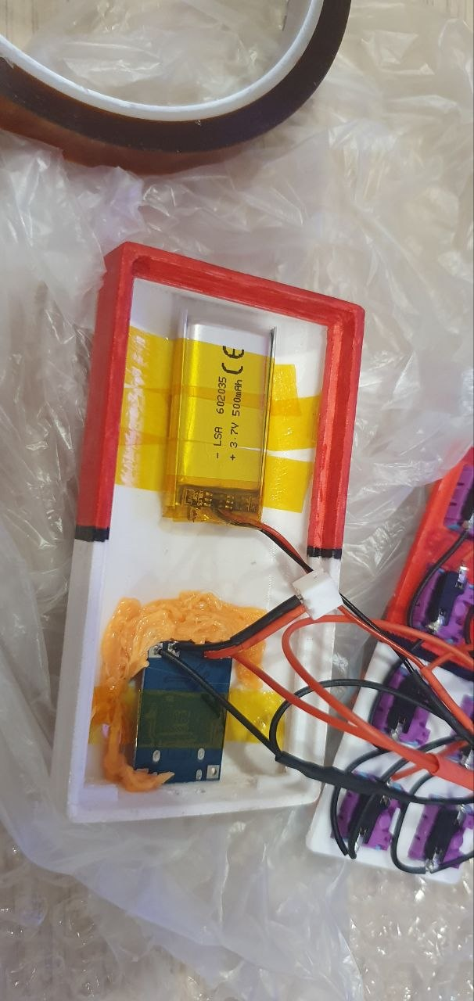
assets/images/64.jpg
