rutony/RutonyPad/assets/images/65.jpg

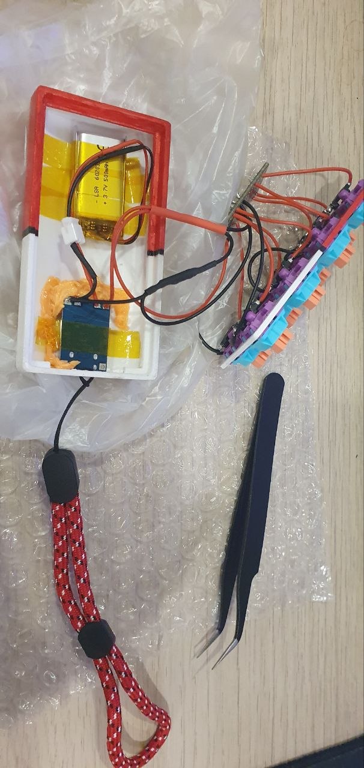
assets/images/65.jpg
