rutony/RutonyPad/assets/images/66.jpg

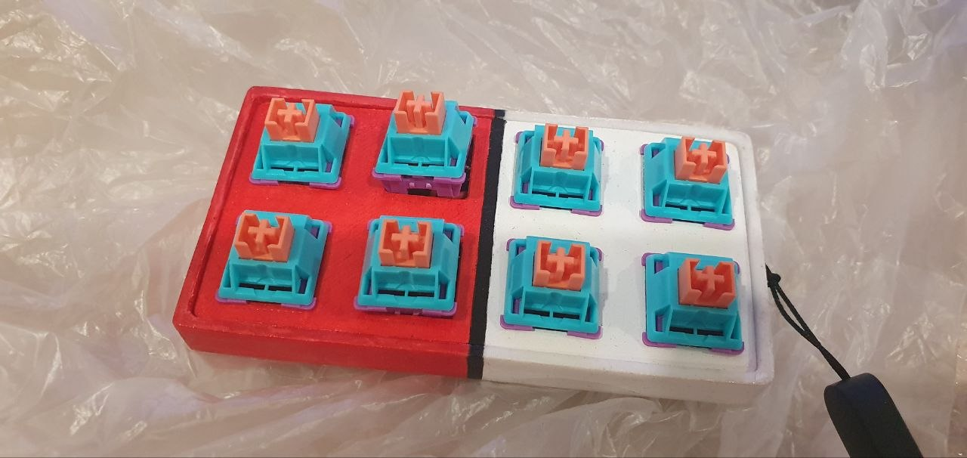
assets/images/66.jpg
