rutony/RutonyPad/assets/images/67.jpg

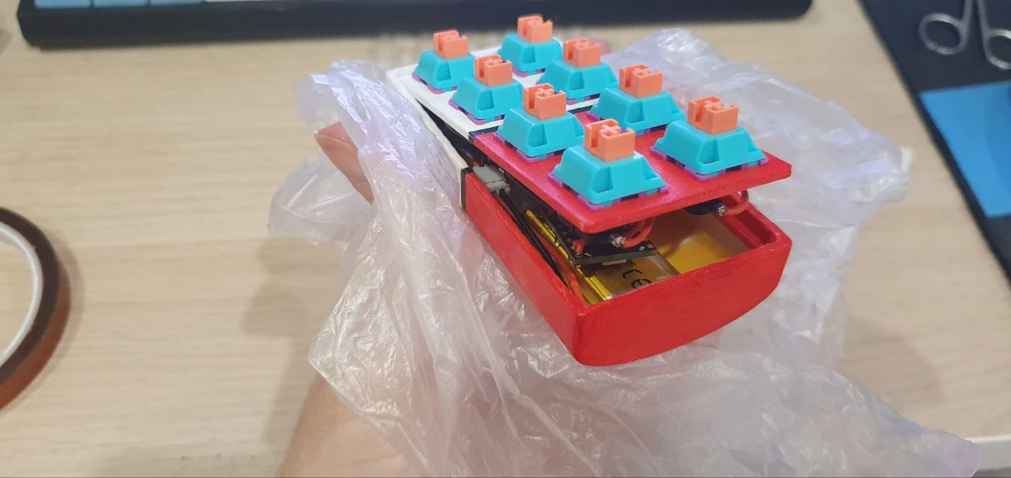
assets/images/67.jpg
