rutony/RutonyPad/assets/images/68.jpg

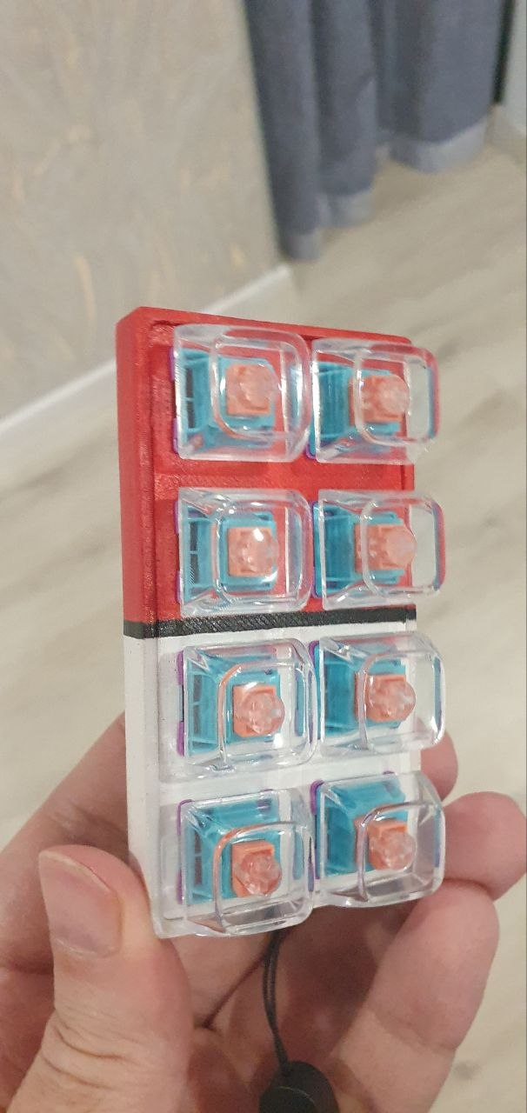
assets/images/68.jpg
