rutony/RutonyPad/assets/images/69.jpg

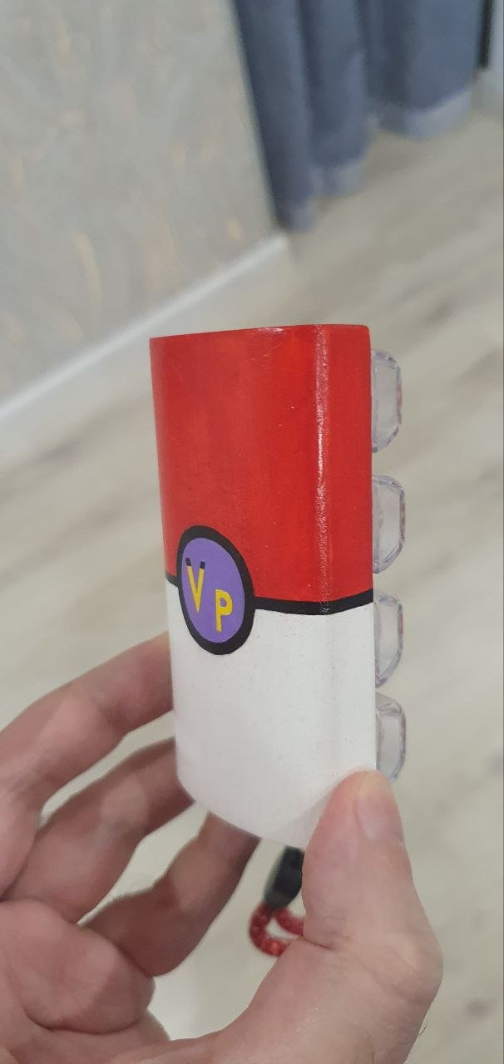
assets/images/69.jpg
