rutony/RutonyPad/assets/images/71.jpg

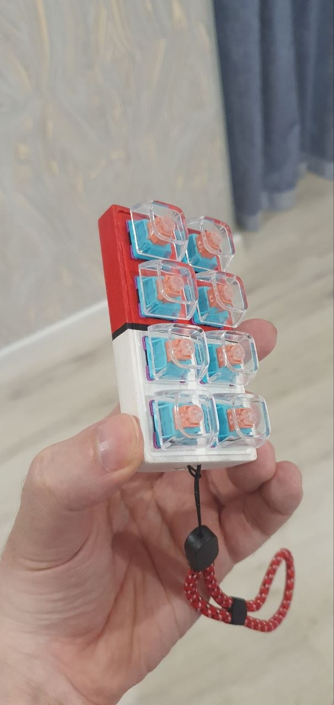
assets/images/71.jpg
