rutony/RutonyPad/assets/images/72.jpg

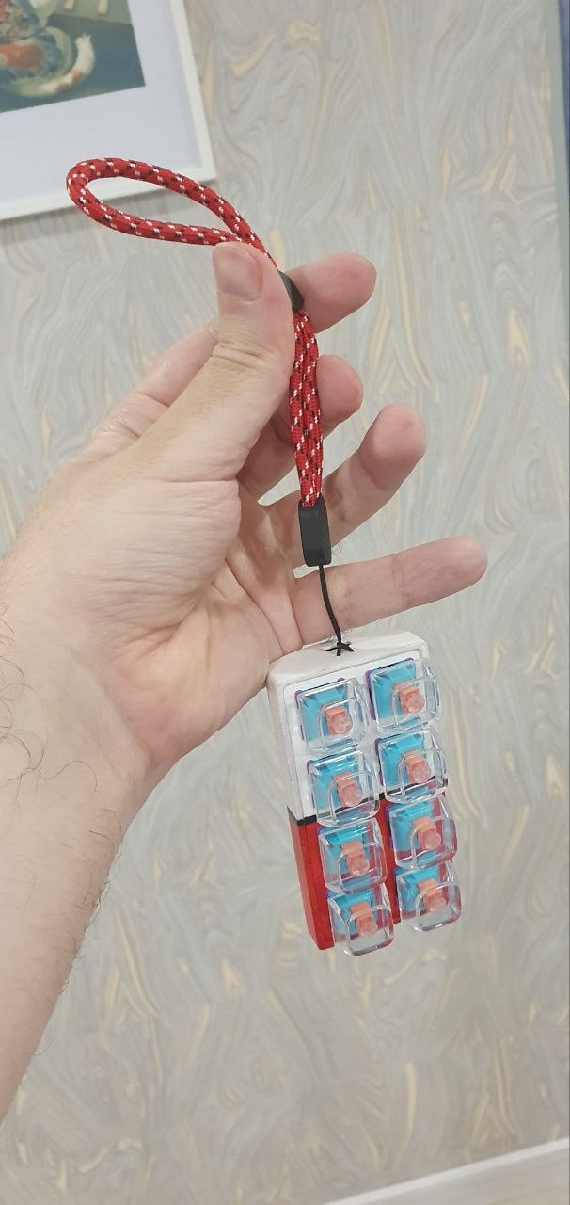
assets/images/72.jpg
