rutony/RutonyPad/assets/images/73.jpg

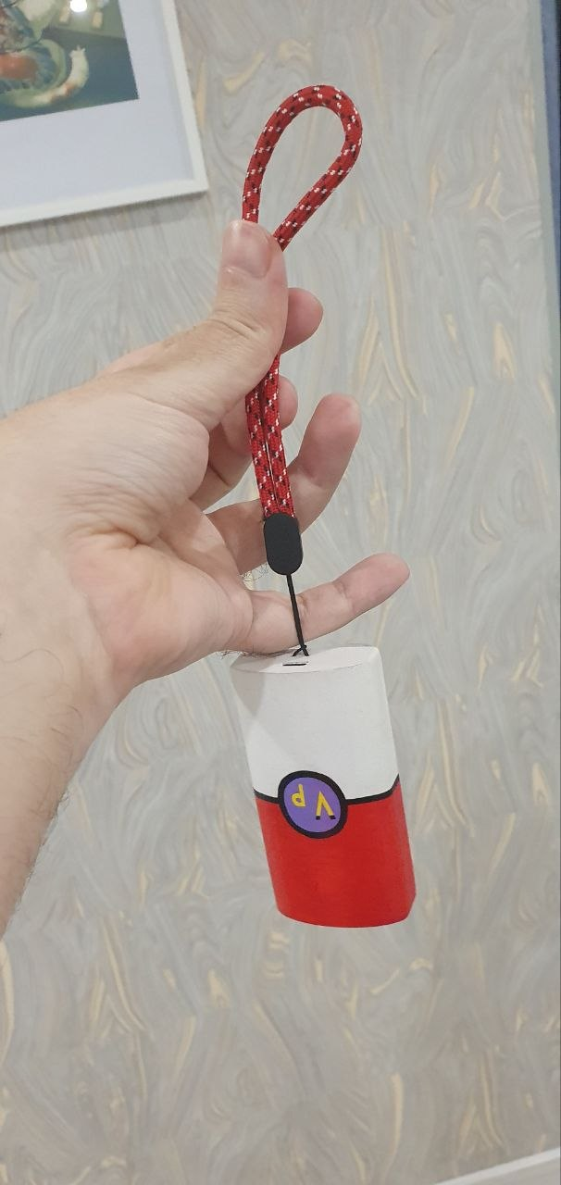
assets/images/73.jpg
