rutony/RutonyPad/assets/images/74.jpg

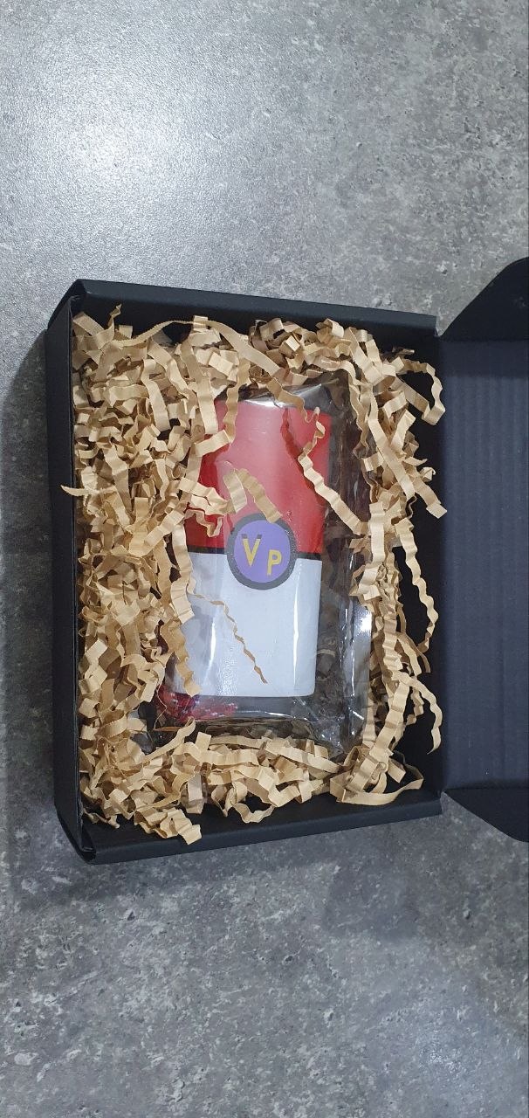
assets/images/74.jpg
