rutony/RutonyPad/assets/images/75.png

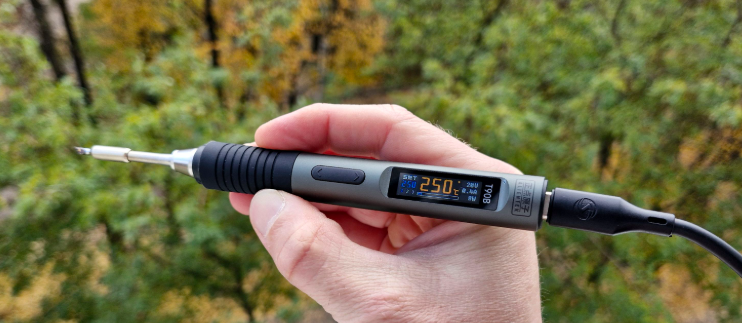
assets/images/75.png
