rutony/RutonyPad/assets/images/Корпус.png

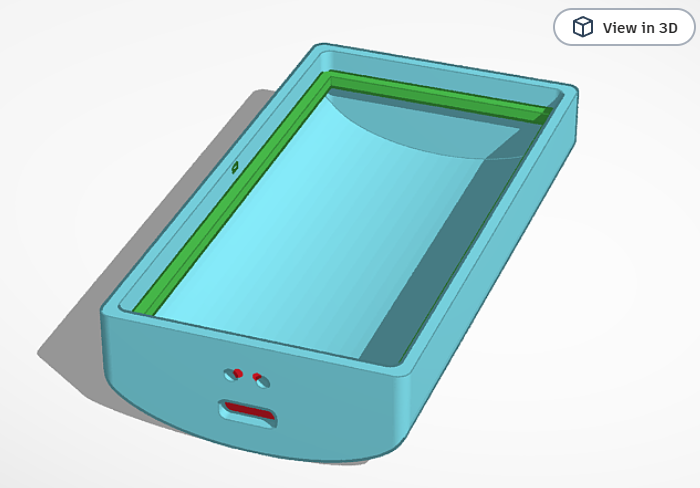
assets/images/Корпус.png
